orje/LEDviaApp/doc/LEDviaApp_UNO_circuit_diagram.png

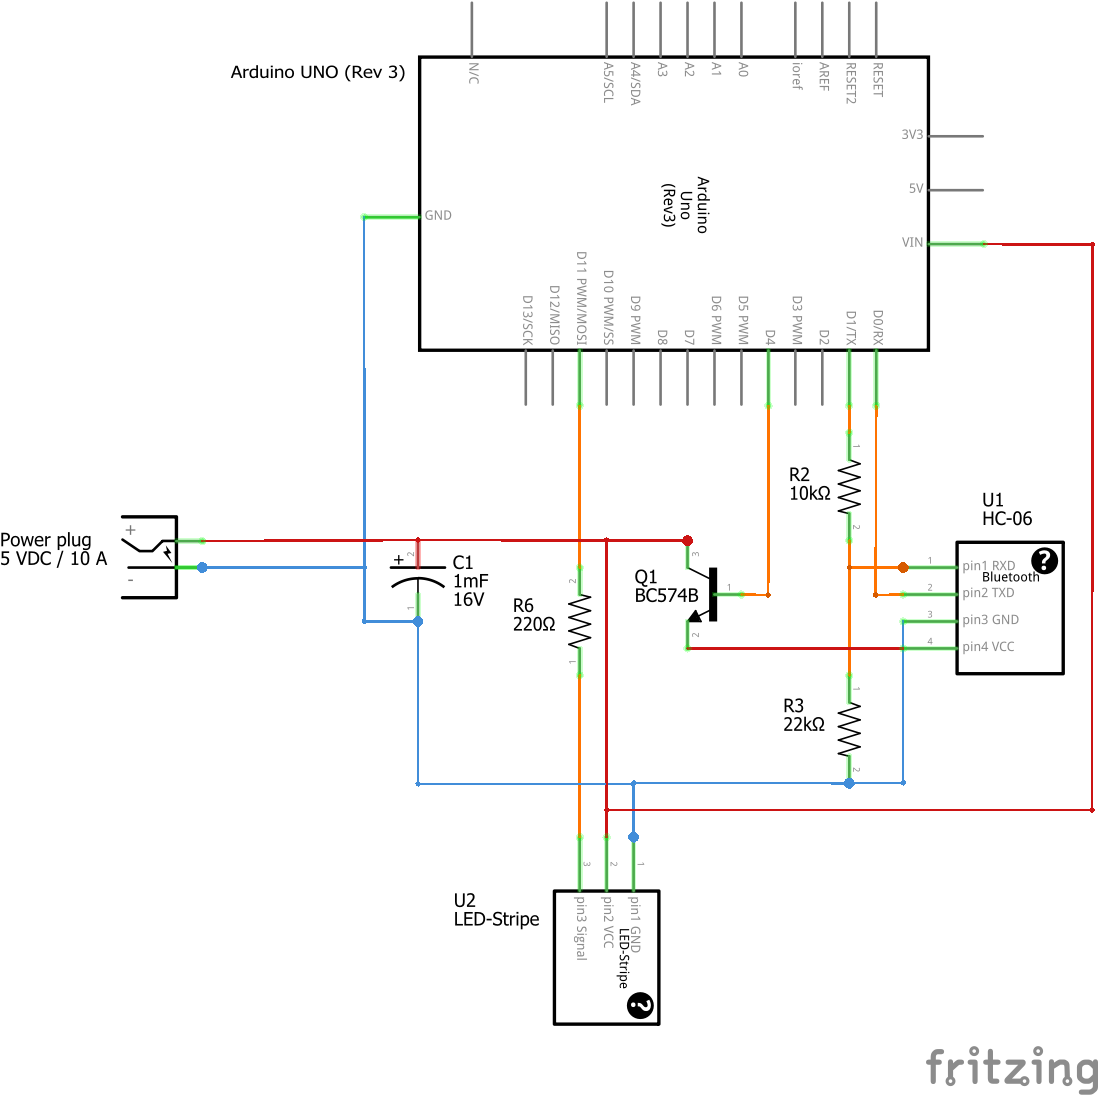
doc/LEDviaApp_UNO_circuit_diagram.png
