orje/LEDviaApp/doc/stuff/App - original.png

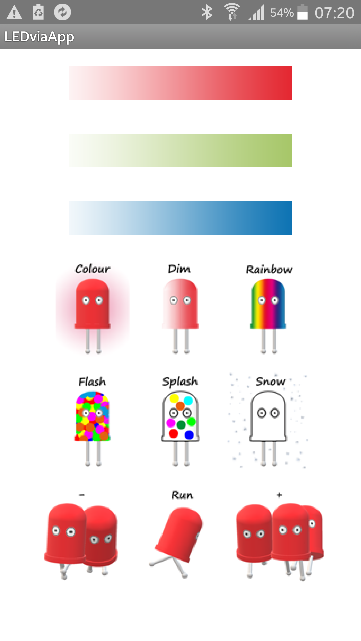
doc/stuff/App - original.png
