orje/LEDviaApp/doc/stuff/LED.jpg

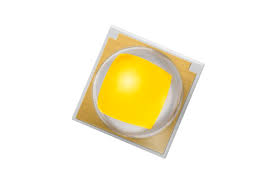
doc/stuff/LED.jpg
