orje/LEDviaApp/doc/stuff/LedManV3/LedManColourV3.png

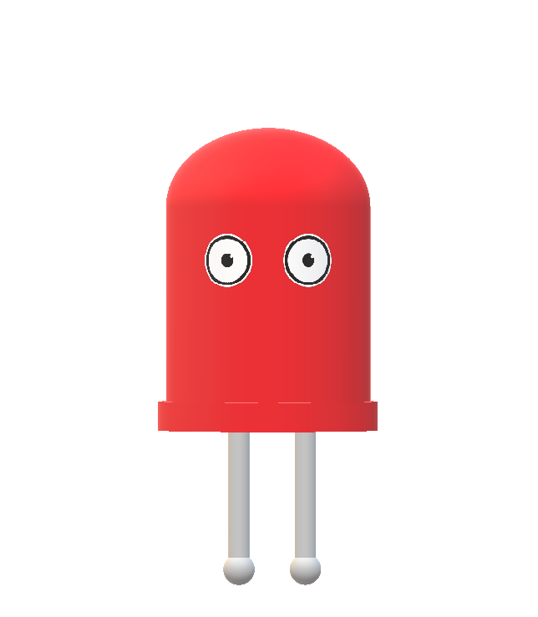
doc/stuff/LedManV3/LedManColourV3.png
