orje/LEDviaApp/doc/stuff/LedManV3/LedManRunMinusV3.png

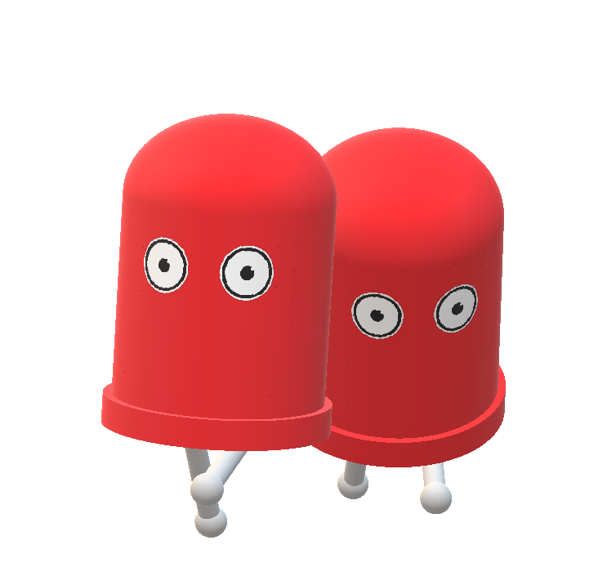
doc/stuff/LedManV3/LedManRunMinusV3.png
