orje/LEDviaApp/doc/stuff/LedManV3/LedManRunPlusV3.png

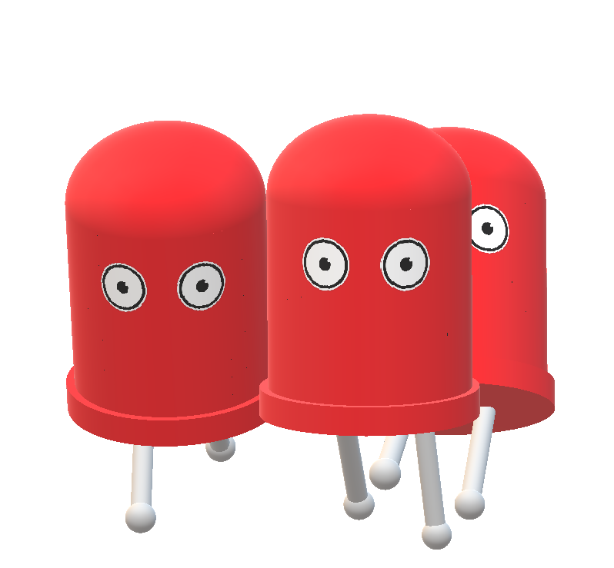
doc/stuff/LedManV3/LedManRunPlusV3.png
