orje/LEDviaApp/doc/stuff/NeoPixels_SPI/SM_of_LEDviaApp.png

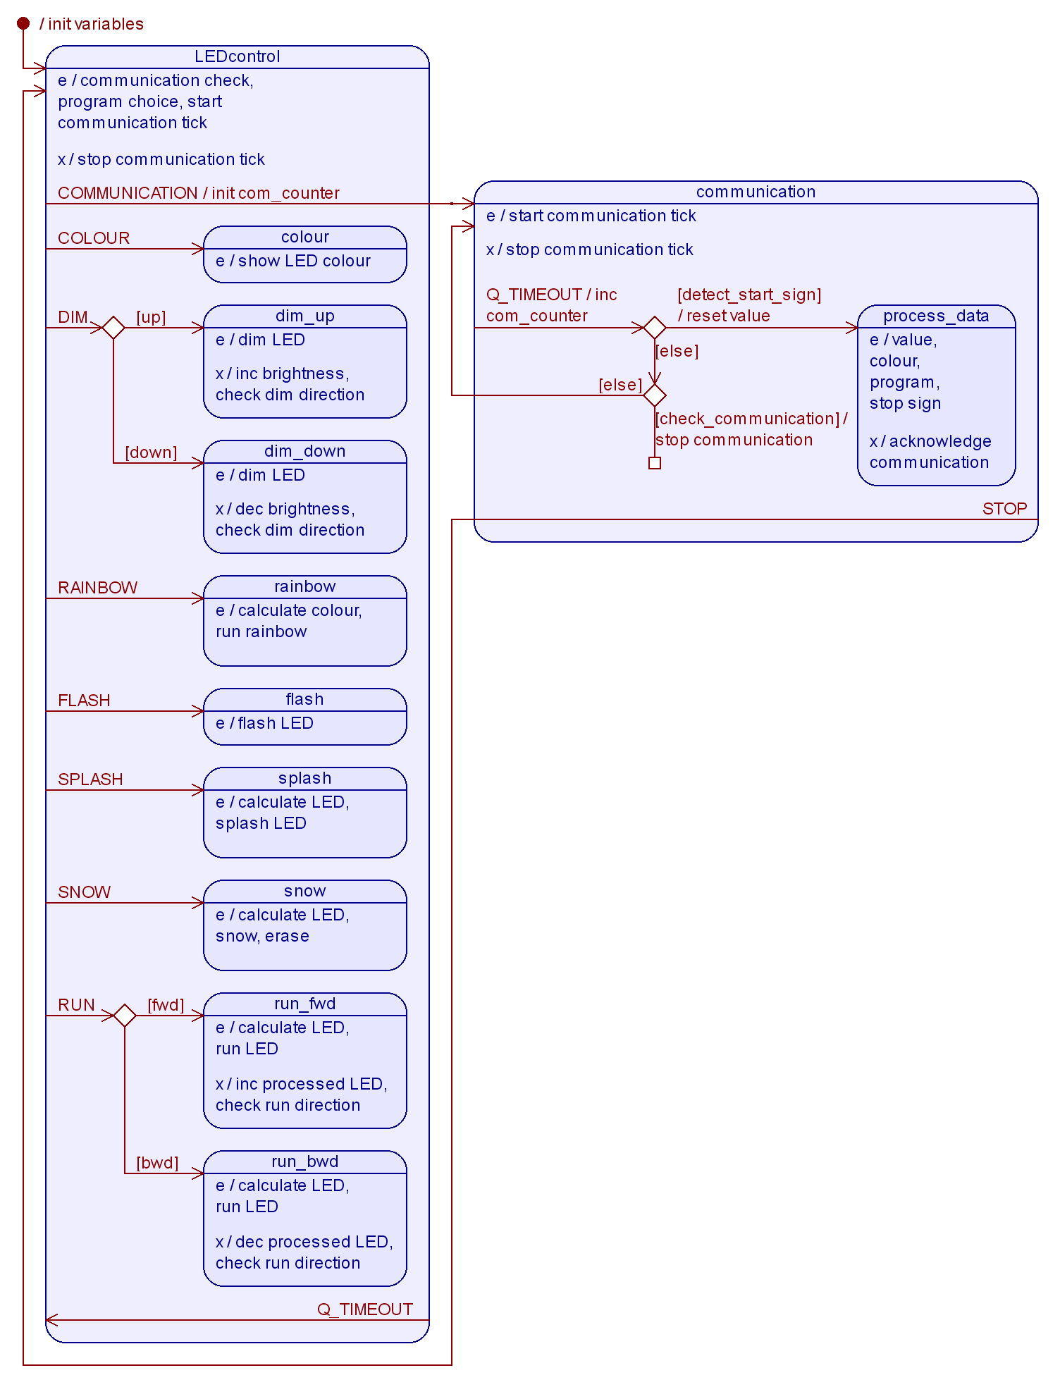
doc/stuff/NeoPixels_SPI/SM_of_LEDviaApp.png
