orje/LEDviaApp/doc/stuff/sketch_directory.PNG

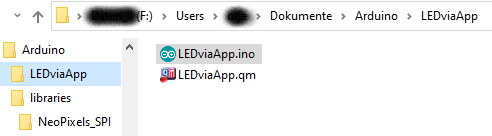
doc/stuff/sketch_directory.PNG
